frindaddy/digichiver/Simulation/speech_filter.asc

C1: cap; 1µF
C2: cap; 10nF
C3: cap; 10nF
C4: cap; 100nF
C5: cap; 100nF
C10: cap; 10µF
R1: res; 100k
R2: res; 100k
R3: res; 2.2k
R4: res; 2.2k
R5: res; 8.2k
R9: res; 100k
R14: res; 8.2k
U1: AD8544
U2: AD8544
U3: AD8544
V1: voltage; 3.3V
V2: voltage; SINE(4.05 1 2000 0 0 0); AC 1
Named nets: 3.3V, 0, speech_out, filtered_out, v_bias
.ac dec 100 10 20k
