frindaddy/digichiver/Software/rom_emulator.py

"""PIO/DMA-backed MM54104 parallel-ROM emulator for the Digichiver board.

No Python executes after ROMEN asserts.  PIO1 turns each ROM request into an
absolute SRAM pointer, DMA fetches the byte, and PIO0 drives RDATA[0..7].
"""

import rp2
import uctypes
from machine import Pin, mem32

ROM_BANK_SIZE = 8 * 1024
ROM_SIZE = 2 * ROM_BANK_SIZE

# Import PIO names only for static type checking; the decorator provides them at runtime.
try:
    import typing
    if typing.TYPE_CHECKING:
        from rp2 import (  # noqa: TC004
            block,
            gpio,
            in_,
            isr,
            jmp,
            label,
            mov,
            osr,
            out,
            pin,
            pins,
            pull,
            push,
            wait,
            wrap,
            wrap_target,
            x,
            x_not_y,
            y,
        )
except ImportError:
    pass

# RP2350 peripheral addresses and register layout.  The DMA channel aliases
# are deliberately used so one DMA channel can arm and trigger the other.
DMA_BASE = 0x50000000
DMA_CH_STRIDE = 0x40
DMA_READ_ADDR = 0x00
DMA_WRITE_ADDR = 0x04
DMA_TRANS_COUNT = 0x08
DMA_CTRL_TRIG = 0x0C
DMA_AL1_CTRL = 0x10
DMA_AL3_READ_ADDR_TRIG = 0x3C
DMA_CH_DBG_CTDREQ_BASE = 0x800
DMA_CHAN_ABORT = 0x464

DMA_CTRL_READ_ERROR = 1 << 30
DMA_CTRL_WRITE_ERROR = 1 << 29
DMA_TRANS_COUNT_TRIGGER_SELF = 1 << 28

PIO0_BASE = 0x50200000
PIO1_BASE = 0x50300000
PIO_TXF0 = PIO0_BASE + 0x10
PIO_RXF0 = PIO1_BASE + 0x20
PIO_FDEBUG = 0x08
# RP2350 adds GPIOBASE after the PIO interrupt register block.  It is not
# adjacent to the FIFO registers as it is tempting to assume from RP2040.
PIO_GPIOBASE = 0x168

# DREQ values are shared by RP2040/RP2350: PIO0 TX0 is 0 and PIO1 RX0 is 12.
DREQ_PIO0_TX0 = 0
DREQ_PIO1_RX0 = 12

DMA_DATA_CHANNEL = 10
DMA_CONTROL_CHANNEL = 11

ROM_ALIGNMENT = ROM_SIZE
RDATA_BASE = 12
ROM_ADDR_BASE = 20
ROMEN_GPIO = 34


def _dma_channel_base(channel: int) -> int:
    """Return the base address of a DMA channel's registers.

    Args:
        channel (int): The DMA channel number.

    Returns:
        int: The base address of the DMA channel's registers.
    """
    return DMA_BASE + channel * DMA_CH_STRIDE

def _dma_ctrl(*, size: int, inc_read: bool, inc_write: bool, treq: int, chain_to: int, ring_size: int=0,
              ring_write: bool=False, high_priority: bool=True) -> int:
    """Build the RP2350 DMA CTRL_TRIG value needed by this emulator.

    Args:
        size (int): The size of each transfer (0=byte, 1=halfword, 2=word).
        inc_read (bool): Whether to increment the read address after each transfer.
        inc_write (bool): Whether to increment the write address after each transfer.
        treq (int): The DREQ value for the DMA channel (0-31).
        chain_to (int): The DMA channel to chain to after this channel completes (0-11).
        ring_size (int, optional): The size of the ring buffer. Defaults to 0.
        ring_write (bool, optional): Whether to write to the ring buffer. Defaults to False.
        high_priority (bool, optional): Whether to give the DMA channel high priority. Defaults to True.

    Returns:
        int: The constructed CTRL_TRIG value for the DMA channel.
    """
    # RP2350 keeps DATA_SIZE and INCR_READ in their RP2040 positions, but
    # inserts INCR_READ_REV and INCR_WRITE_REV.  INCR_WRITE and every field
    # above it therefore move.  See RP2350 datasheet table 1151.
    value = 1  # EN
    value |= int(high_priority) << 1
    value |= size << 2
    value |= int(inc_read) << 4
    value |= int(inc_write) << 6
    value |= ring_size << 8
    value |= int(ring_write) << 12
    value |= chain_to << 13
    value |= treq << 17
    value |= 1 << 23  # IRQ_QUIET: this streaming path does not need IRQs.
    return value

def _load_rom(target: memoryview, rom_paths: tuple) -> None:
    """Load one image or two 8 KiB banks into a writable 16 KiB buffer.

    Args:
        target (memoryview): The writable 16 KiB ROM buffer.
        rom_paths (tuple): One image path or two 8 KiB bank paths.
    """
    if len(target) != ROM_SIZE:
        raise ValueError(f"ROM target must be exactly {ROM_SIZE} bytes")

    if len(rom_paths) == 1:
        for index in range(ROM_SIZE):
            target[index] = 0
        _read_into(target, rom_paths[0], ROM_SIZE, allow_short=True)
        return
    if len(rom_paths) != 2:
        raise ValueError("ROM source must contain one or two paths")

    view = memoryview(target)
    _read_into(view[:ROM_BANK_SIZE], rom_paths[0], ROM_BANK_SIZE)
    _read_into(view[ROM_BANK_SIZE:], rom_paths[1], ROM_BANK_SIZE)


def _read_into(
    target: memoryview,
    path: str,
    expected_size: int,
    allow_short: bool=False,
) -> None:
    """Read a ROM file into a buffer, rejecting invalid file sizes.

    Args:
        target (memoryview): The writable destination buffer.
        path (str): The ROM file path.
        expected_size (int): The required destination size.
        allow_short (bool, optional): Allow a non-empty file shorter than the destination. Defaults to False.
    """
    with open(path, "rb") as rom_file:
        bytes_read = rom_file.readinto(target)
        if allow_short and bytes_read:
            if rom_file.read(1):
                raise ValueError(f"{path} must not exceed {ROM_SIZE} bytes")
            return
        if bytes_read != expected_size:
            raise ValueError(f"{path} must contain exactly {expected_size} bytes")
        if rom_file.read(1):
            if expected_size == ROM_SIZE:
                raise ValueError(f"{path} must not exceed {ROM_SIZE} bytes")
            raise ValueError(f"{path} must contain exactly {expected_size} bytes")

@rp2.asm_pio(in_shiftdir=rp2.PIO.SHIFT_LEFT)
def _capture_request() -> None:
    """Push an absolute SRAM address whenever the active ROM address changes."""
    pull(block)
    # OSR permanently holds the SRAM base address divided by 16 KiB.  X is
    # the last absolute address served and Y is the current address.
    wrap_target()
    label("idle")
    wait(0, gpio, 2)            # System GPIO34 with PIO GPIOBASE=16.
    mov(isr, osr)
    in_(pins, 14)               # GPIO20..33, relative to GPIO base 16.
    mov(x, isr)
    push(block)                 # Always serve the first address after ROMEN.

    label("active")
    jmp(pin, "idle")            # ROMEN high: wait for the next assertion.
    mov(isr, osr)
    in_(pins, 14)
    mov(y, isr)
    jmp(x_not_y, "changed")
    jmp("active")

    label("changed")
    mov(x, y)
    mov(isr, y)
    push(block)
    jmp("active")
    wrap()

@rp2.asm_pio(
    out_shiftdir=rp2.PIO.SHIFT_RIGHT,
    out_init=(rp2.PIO.OUT_LOW,) * 8, # type: ignore
)
def _drive_data() -> None:
    """Consume one DMA word and present its low byte on RDATA[0..7]."""
    wrap_target()
    pull(block)
    out(pins, 8)
    wrap()

class RomEmulator:
    """Serve a ROM image as the MM54104's 16 KiB parallel ROM."""

    def __init__(self) -> None:
        self._allocation = None
        self._rom = None
        self._rom_address = None
        self._capture_sm = None
        self._output_sm = None
        self.running = False

    def _abort_dma_channels(self) -> None:
        """Put both reserved DMA channels into a known idle state."""
        channels = (DMA_DATA_CHANNEL, DMA_CONTROL_CHANNEL)
        mask = (1 << DMA_DATA_CHANNEL) | (1 << DMA_CONTROL_CHANNEL)

        for channel in channels:
            # EN=0 pauses the channel; CHAIN_TO=self disables chaining.  The
            # two error bits are write-one-to-clear.
            mem32[_dma_channel_base(channel) + DMA_CTRL_TRIG] = (
                DMA_CTRL_READ_ERROR
                | DMA_CTRL_WRITE_ERROR
                | (channel << 13)
            )

        mem32[DMA_BASE + DMA_CHAN_ABORT] = mask
        for _ in range(100_000):
            if not (mem32[DMA_BASE + DMA_CHAN_ABORT] & mask):
                break
        else:
            raise RuntimeError("DMA channels 10/11 did not abort")

        # Reset accumulated DREQ credits and re-initiate each handshake.
        for channel in channels:
            mem32[
                DMA_BASE + DMA_CH_DBG_CTDREQ_BASE + channel * DMA_CH_STRIDE
            ] = 0

    def _configure_dma(self) -> None:
            """Configure the two reserved DMA channels for the ROM emulator."""
            data = _dma_channel_base(DMA_DATA_CHANNEL)
            control = _dma_channel_base(DMA_CONTROL_CHANNEL)
    
            # A MicroPython soft reset does not necessarily reset the DMA block.
            # Clearing EN only pauses a BUSY channel, so an old endless transfer
            # would ignore all triggers below.  Abort both sides of the pipeline
            # together, as required by RP2350 datasheet section 12.6.8.3.
            self._abort_dma_channels()
    
            # Clear FIFO error flags left by an earlier configuration.
            mem32[PIO0_BASE + PIO_FDEBUG] = 0xFFFFFFFF
            mem32[PIO1_BASE + PIO_FDEBUG] = 0xFFFFFFFF
    
            # The data channel is dormant until control DMA writes READ_ADDR_TRIG.
            # Its reload count remains one, so every trigger fetches one byte.  A
            # byte-wide peripheral write replicates the byte in the PIO FIFO word;
            # _drive_data always shifts out its low eight bits.
            mem32[data + DMA_READ_ADDR] = self._rom_address
            mem32[data + DMA_WRITE_ADDR] = PIO_TXF0
            mem32[data + DMA_TRANS_COUNT] = 1
            # AL1_CTRL is a non-triggering alias, leaving this channel armed but
            # dormant until the first address arrives from the control channel.
            mem32[data + DMA_AL1_CTRL] = _dma_ctrl(
                size=0, inc_read=False, inc_write=False, treq=DREQ_PIO0_TX0,
                chain_to=DMA_DATA_CHANNEL,
            )
    
            # Each request is one absolute address.  Writing it directly to the
            # data channel's AL3_READ_ADDR_TRIG alias reloads COUNT=1 and starts
            # the byte fetch.
            mem32[control + DMA_READ_ADDR] = PIO_RXF0
            mem32[control + DMA_WRITE_ADDR] = data + DMA_AL3_READ_ADDR_TRIG
            mem32[control + DMA_TRANS_COUNT] = DMA_TRANS_COUNT_TRIGGER_SELF | 1
            mem32[control + DMA_CTRL_TRIG] = _dma_ctrl(
                size=2, inc_read=False, inc_write=False, treq=DREQ_PIO1_RX0,
                chain_to=DMA_CONTROL_CHANNEL,
            )

    def _stage_rom(self, rom_paths: tuple) -> tuple:
        """Allocate, align, and populate a ROM image before publication.

        Args:
            rom_paths (tuple): One image path or two 8 KiB bank paths.

        Returns:
            tuple: The backing allocation, aligned ROM view, and ROM address.
        """
        # PIO creates the DMA source address by replacing the low 14 bits, so
        # the backing image must begin on a 16 KiB boundary.
        allocation = bytearray(ROM_SIZE + ROM_ALIGNMENT - 1)
        allocation_address = uctypes.addressof(allocation)
        offset = (-allocation_address) & (ROM_ALIGNMENT - 1)
        rom = memoryview(allocation)[offset:offset + ROM_SIZE]
        _load_rom(rom, rom_paths)

        rom_address = uctypes.addressof(rom)
        if rom_address & (ROM_ALIGNMENT - 1):
            raise RuntimeError("unable to allocate a 16 KiB-aligned ROM image")
        return allocation, rom, rom_address

    def load(self, *rom_paths: str) -> None:
        """Stage one image or two banks, then start the emulator.

        Files are fully validated before an existing running image is stopped.
        If starting the staged image fails, the emulator is stopped and the
        staged image remains selected.

        Args:
            *rom_paths (str): One image path or two 8 KiB bank paths.
        """
        if len(rom_paths) not in (1, 2):
            raise ValueError("ROM source must contain one or two paths")

        allocation, rom, rom_address = self._stage_rom(rom_paths)
        if self.running:
            self.stop()
        self._allocation = allocation  # Keep the DMA buffer alive and fixed.
        self._rom = rom
        self._rom_address = rom_address
        print(f"ROM loaded from {rom_paths}, aligned at 0x{rom_address:08X}")
        try:
            self.start()
        except Exception:
            self.stop()
            raise

    def start(self) -> None:
        """Arm PIO and DMA. Call load() successfully before start()."""
        if self.running:
            return
        if self._rom is None:
            raise RuntimeError("call load() before start()")

        # The bus is not tri-stated by the fitted always-enabled level shifter;
        # make its inactive value known until the first ROM transaction.
        for gpio in range(RDATA_BASE, RDATA_BASE + 8):
            Pin(gpio, Pin.OUT, value=0)
        for gpio in range(ROM_ADDR_BASE, ROMEN_GPIO + 1):
            Pin(gpio, Pin.IN)

        # PIO0 handles GPIO12..19 with base 0.  PIO1 handles GPIO20..34 with
        # base 16, allowing both the 14-bit address bus and ROMEN in one SM.
        mem32[PIO0_BASE + PIO_GPIOBASE] = 0
        mem32[PIO1_BASE + PIO_GPIOBASE] = 16
        self._output_sm = rp2.StateMachine(
            0, _drive_data, freq=150_000_000, out_base=Pin(RDATA_BASE)
        )
        self._capture_sm = rp2.StateMachine(
            4, _capture_request, freq=150_000_000,
            in_base=Pin(ROM_ADDR_BASE), jmp_pin=Pin(ROMEN_GPIO)
        )

        self._configure_dma()
        self._output_sm.active(1)
        self._capture_sm.put(self._rom_address >> 14) # type: ignore
        self._capture_sm.active(1)
        self.running = True

    def stop(self) -> None:
        """Disable request generation before stopping the DMA pipeline."""
        if self._capture_sm is not None:
            self._capture_sm.active(0)
        if self._output_sm is not None:
            self._output_sm.active(0)
        self._abort_dma_channels()
        for state_machine in (self._capture_sm, self._output_sm):
            deinit = getattr(state_machine, "deinit", None)
            if deinit is not None:
                deinit()
        self._capture_sm = None
        self._output_sm = None
        self.running = False
